PDunham113/UCONN-SDP-1611/Doc/PCBs/LCD Rev. 2 Gerber.PNG

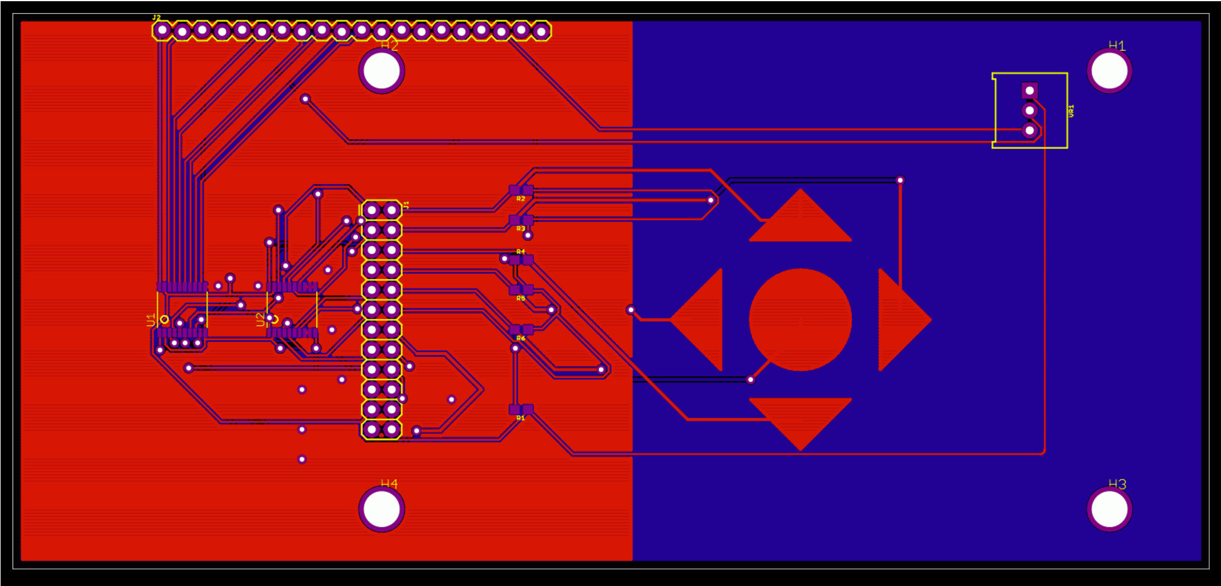
Doc/PCBs/LCD Rev. 2 Gerber.PNG
