PDunham113/UCONN-SDP-1611/Doc/PCBs/Relay Rev. 1 Back.PNG

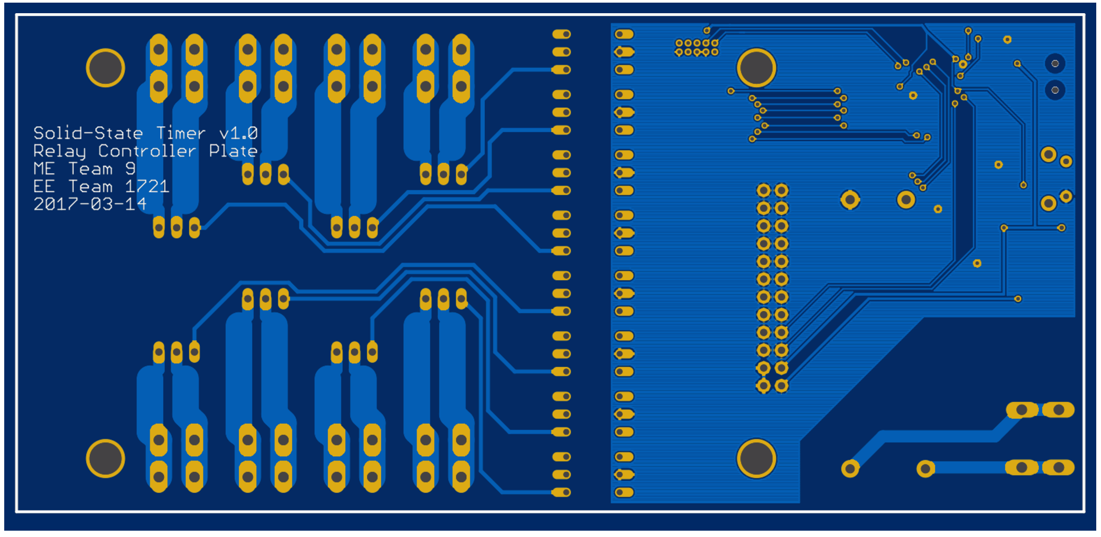
Doc/PCBs/Relay Rev. 1 Back.PNG
