PDunham113/UCONN-SDP-1611/Doc/PCBs/Relay Rev. 2 Back.PNG

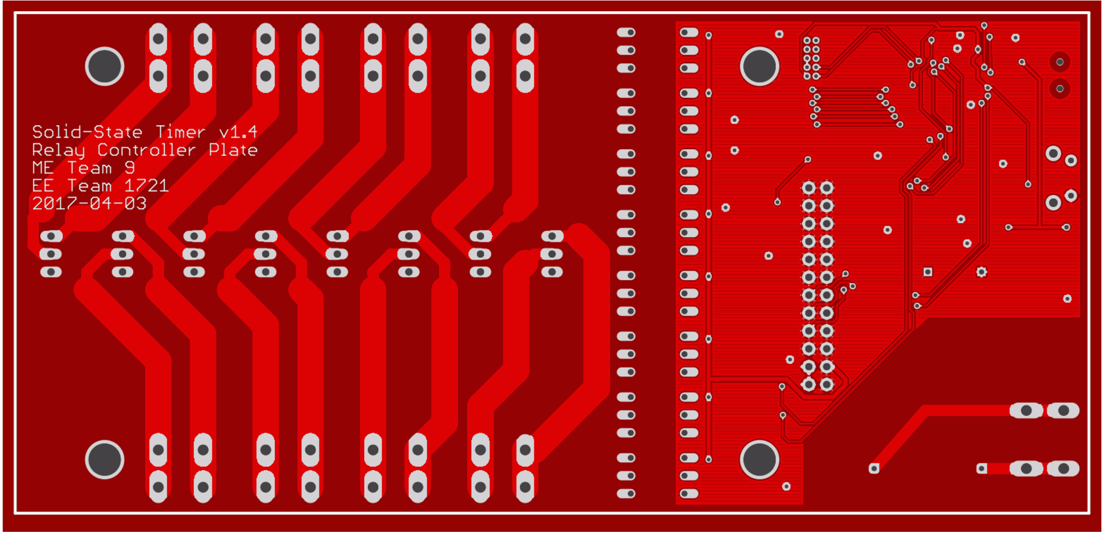
Doc/PCBs/Relay Rev. 2 Back.PNG
