PDunham113/UCONN-SDP-1611/Microcontroller/Microcontroller 1.1 Brd.png

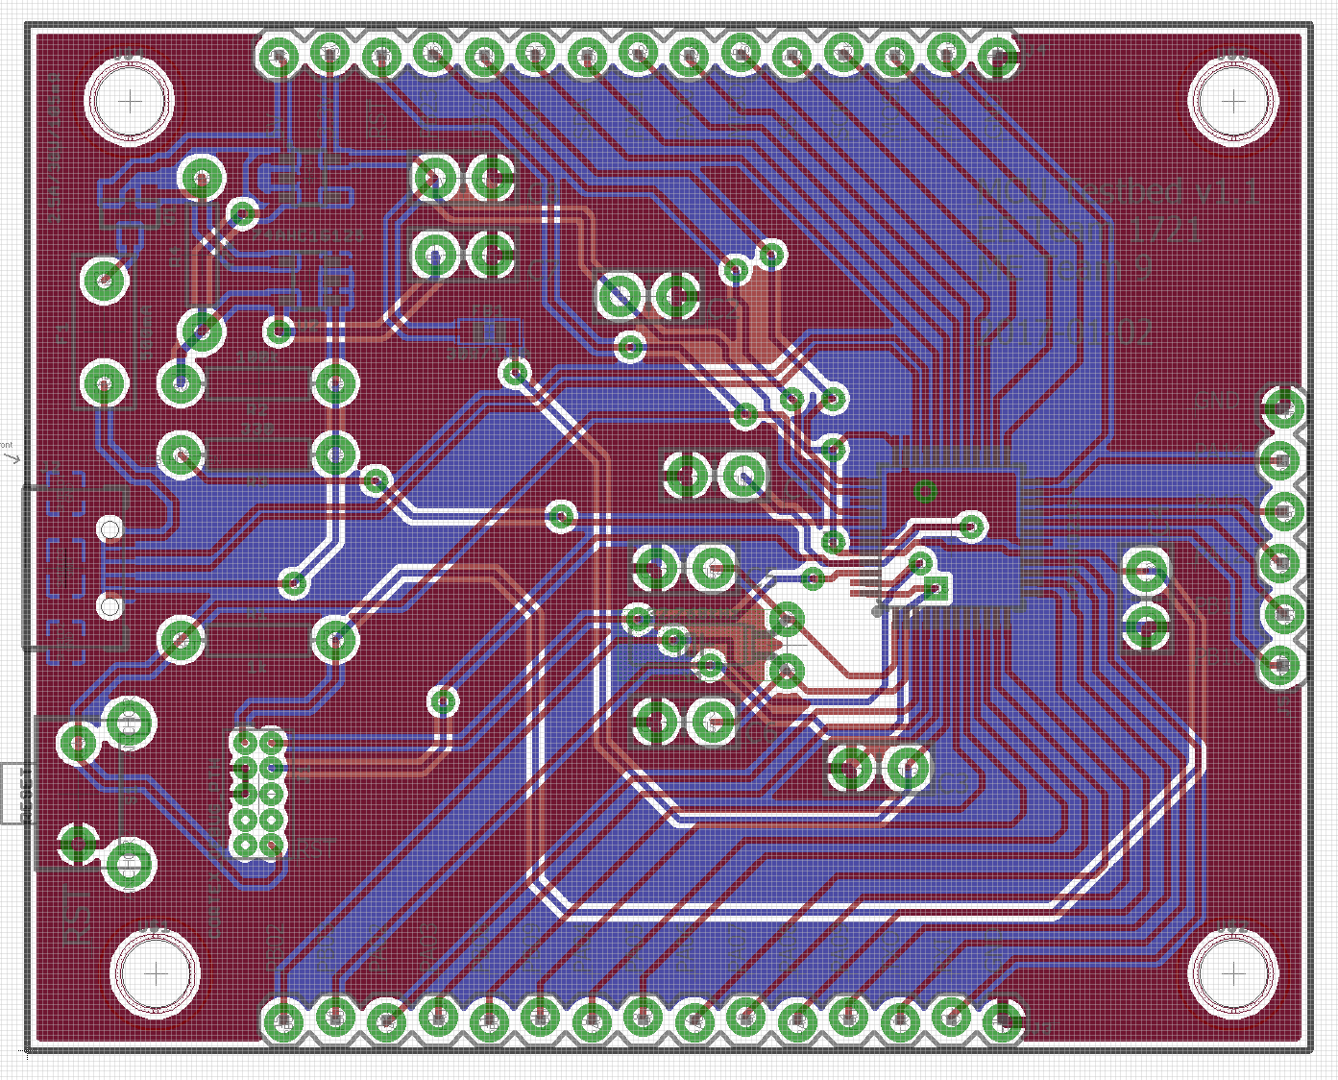
Microcontroller/Microcontroller 1.1 Brd.png
