PDunham113/UCONN-SDP-1611/Microcontroller/Microcontroller 1.1 Sch.png

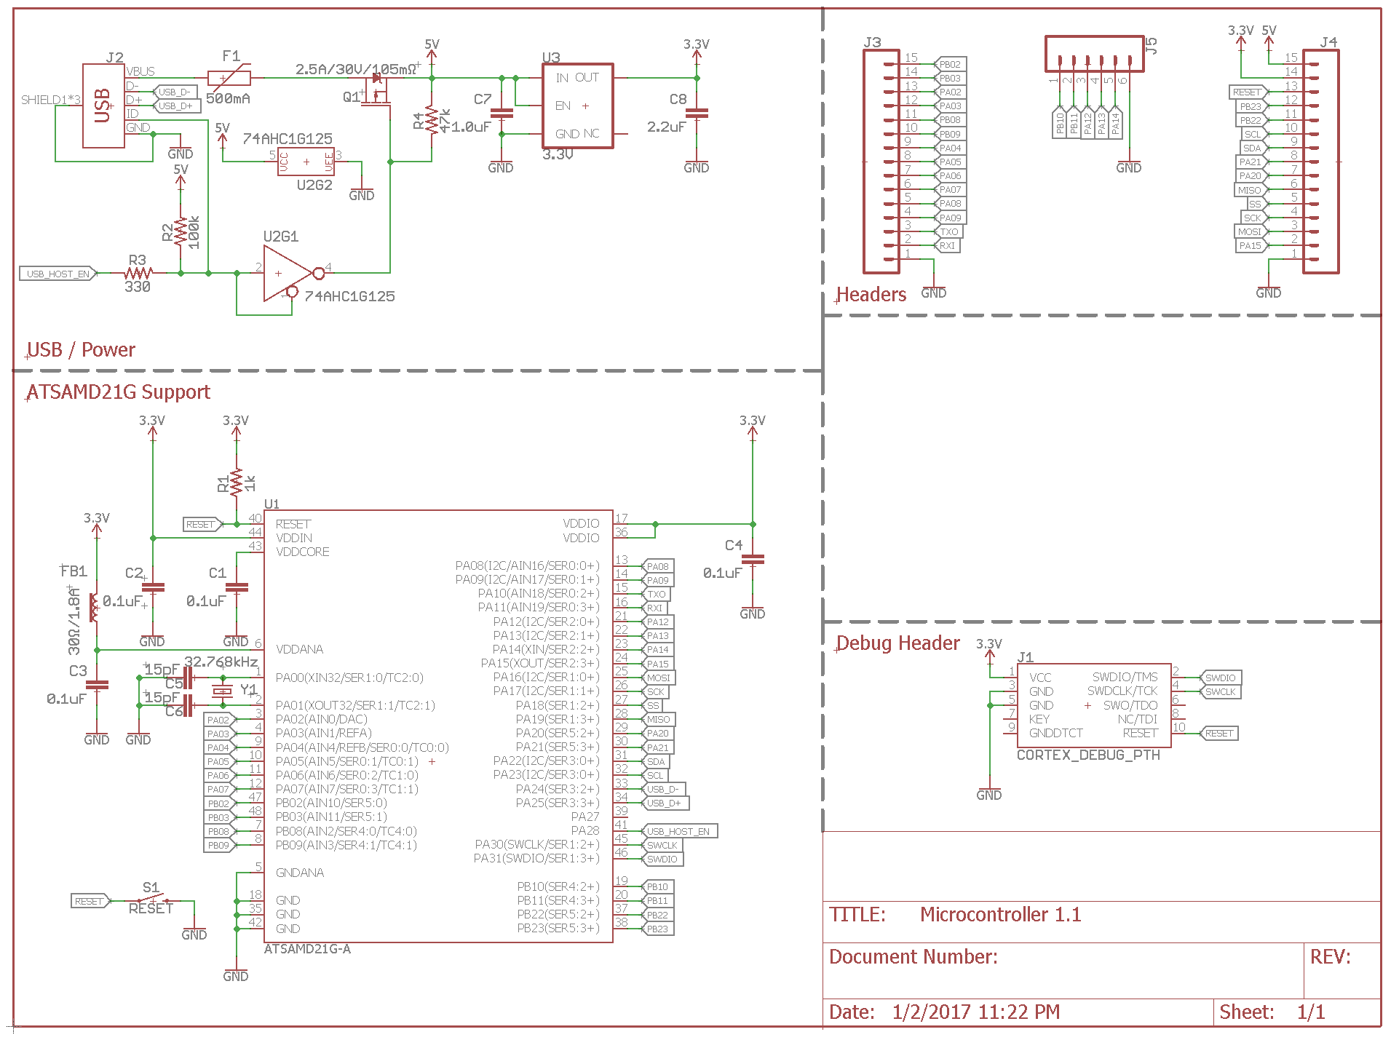
Microcontroller/Microcontroller 1.1 Sch.png
