PDunham113/UCONN-SDP-1611/Solid State Relay/Solid State Relay Sch v1.1.PNG

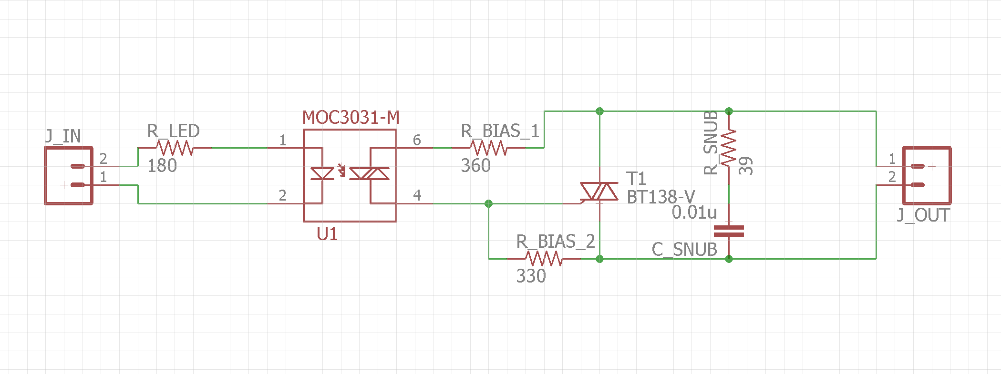
Solid State Relay/Solid State Relay Sch v1.1.PNG
